IRNAS/ServalRuggedBatteryPack/enclosure/capture1.png

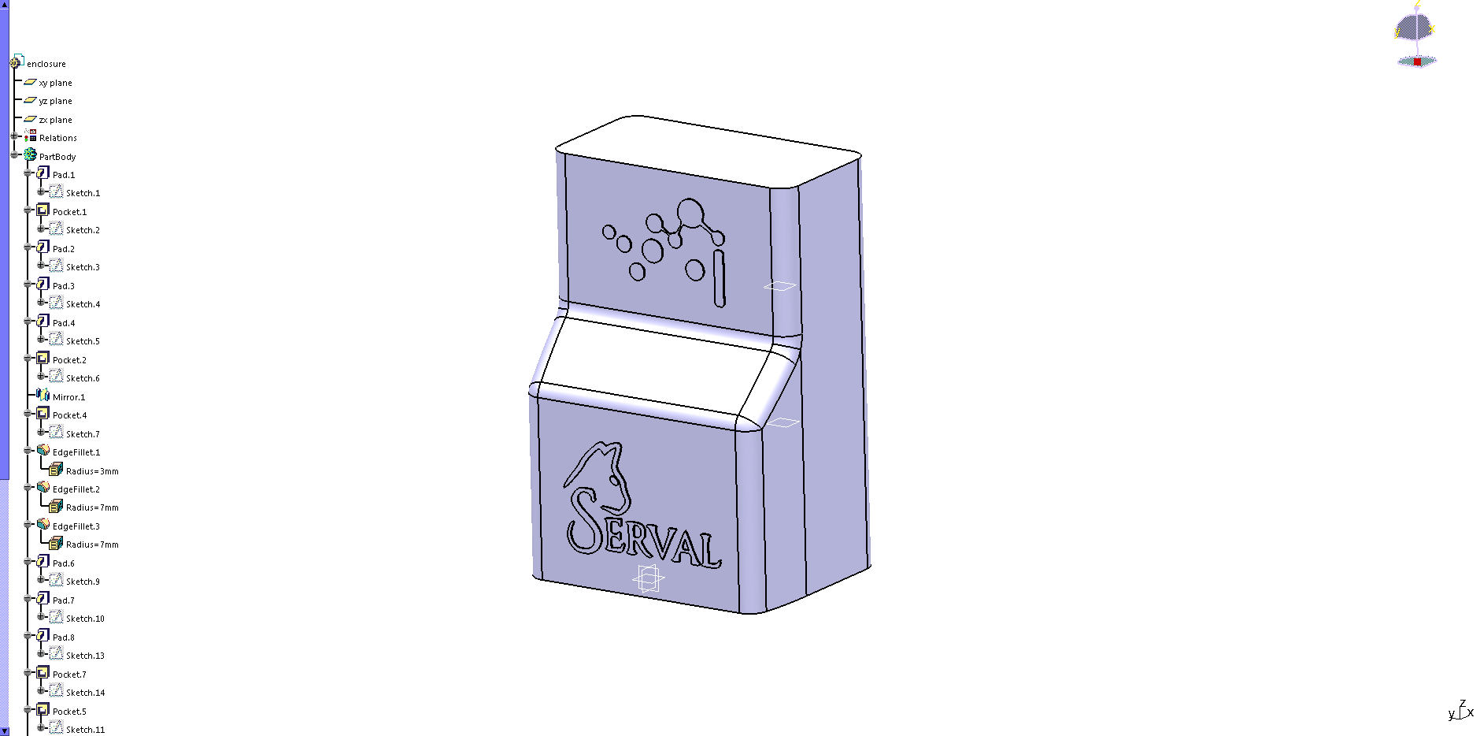
enclosure/capture1.png
