IRNAS/ServalRuggedBatteryPack/enclosure/capture2.png

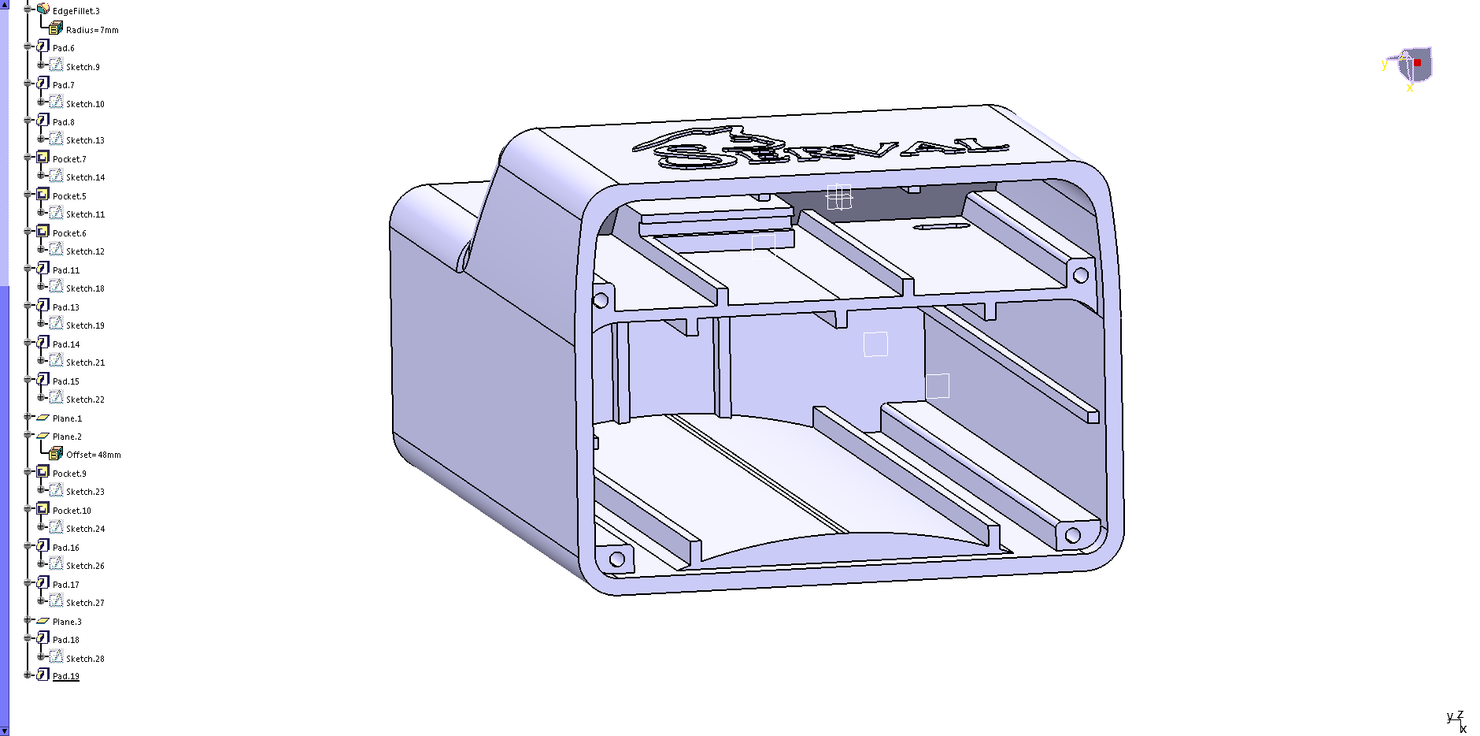
enclosure/capture2.png
